The-C6H6/PLANTA-DE-ANILINA/PID/PDF/ENFRIADOR PRIMERA COLUMNA.pdf

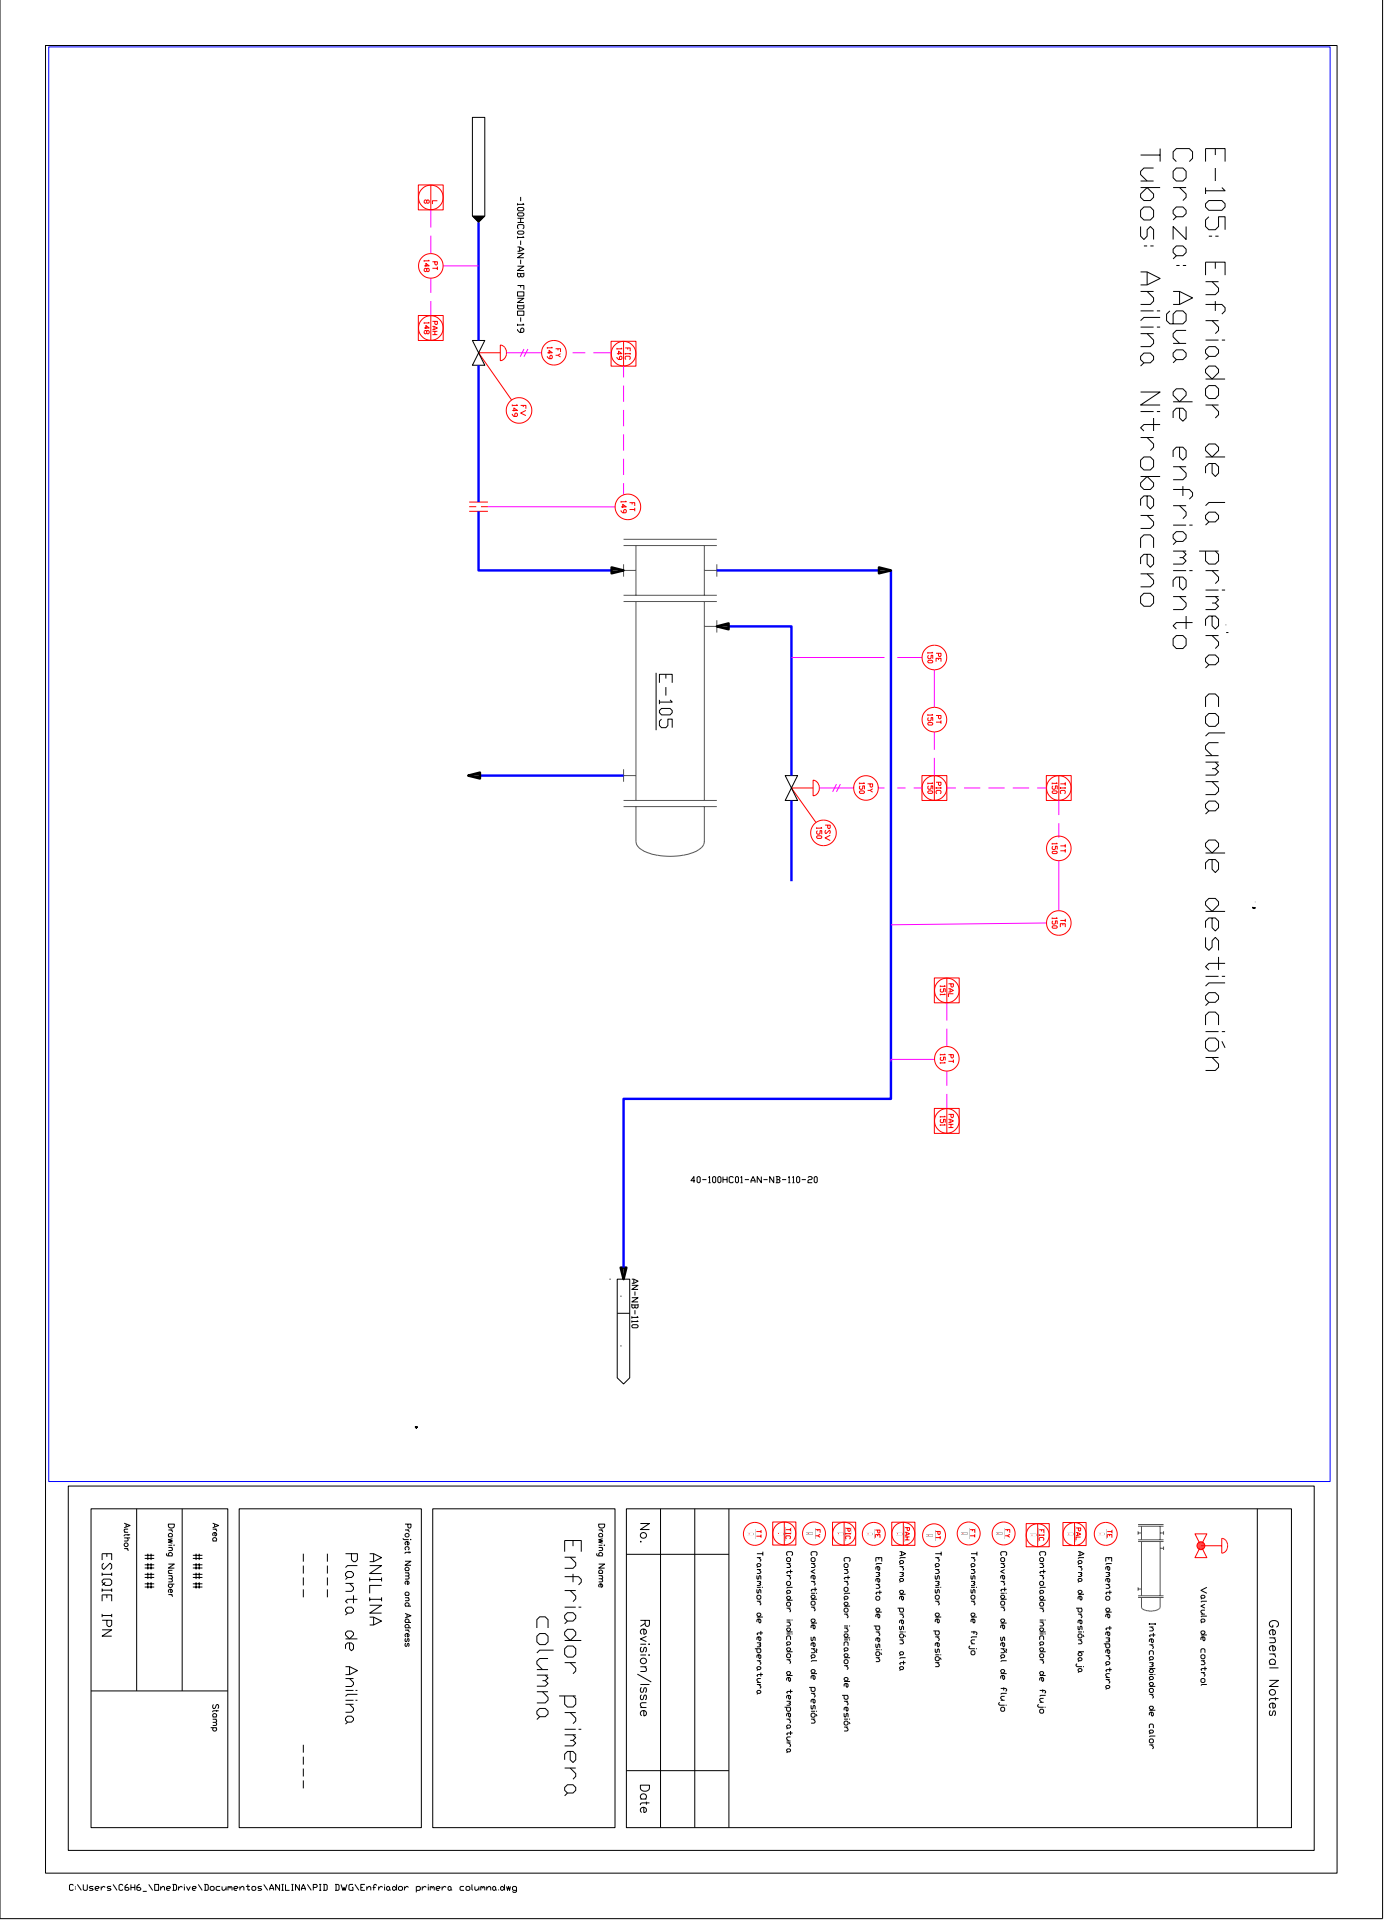
[picture p12: page 1]
