The-C6H6/PLANTA-DE-ANILINA/PID/PDF/INTERCAMBIADOR DE H2.pdf

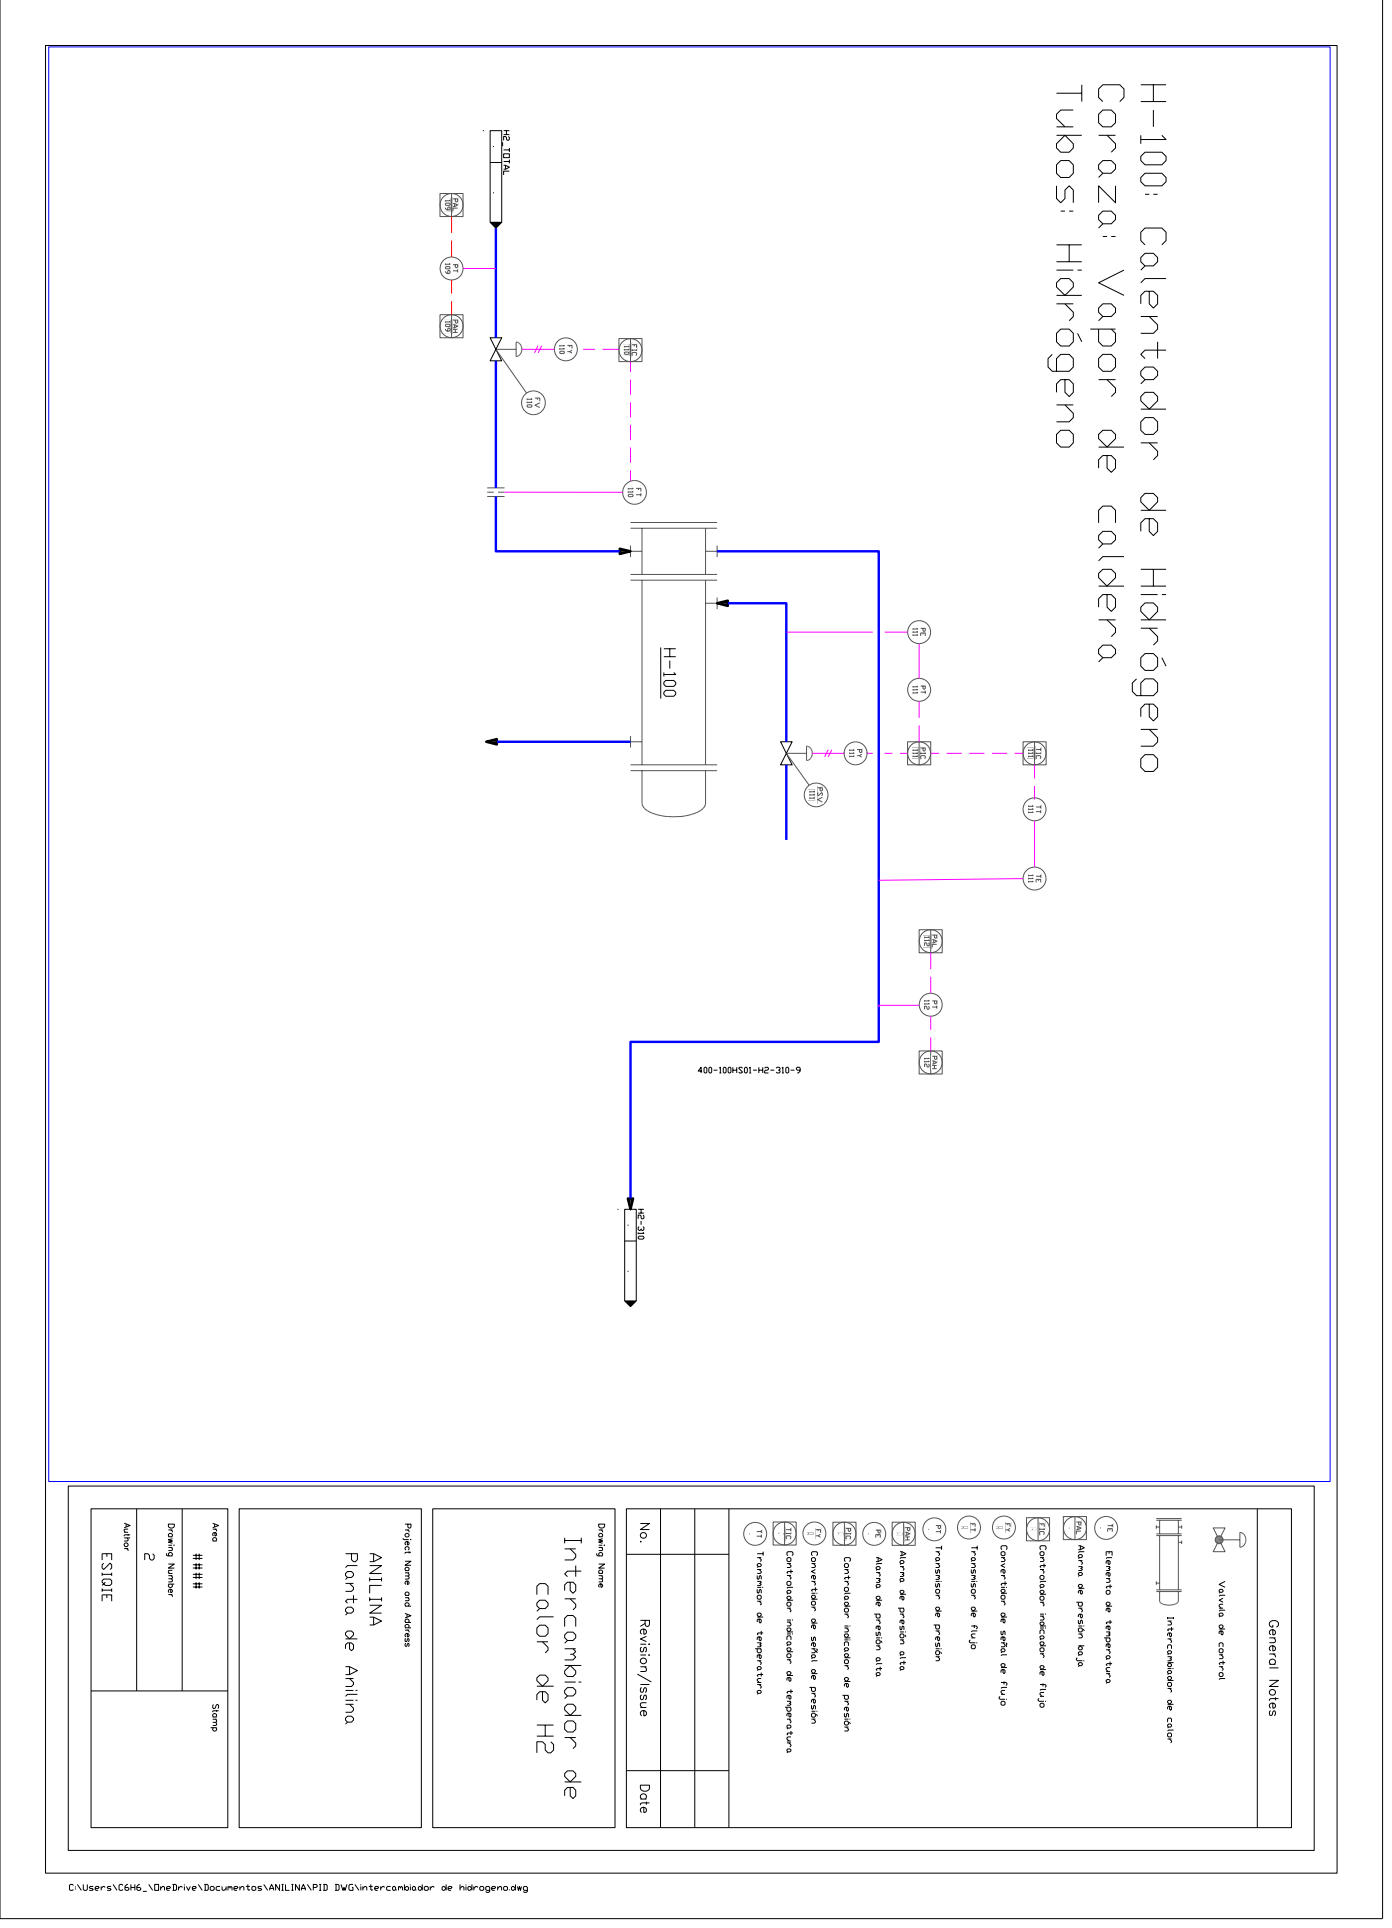
[picture p13: page 1]
