The-C6H6/PLANTA-DE-ANILINA/PID/PDF/INTERCAMBIADOR DE MEZCLA.pdf

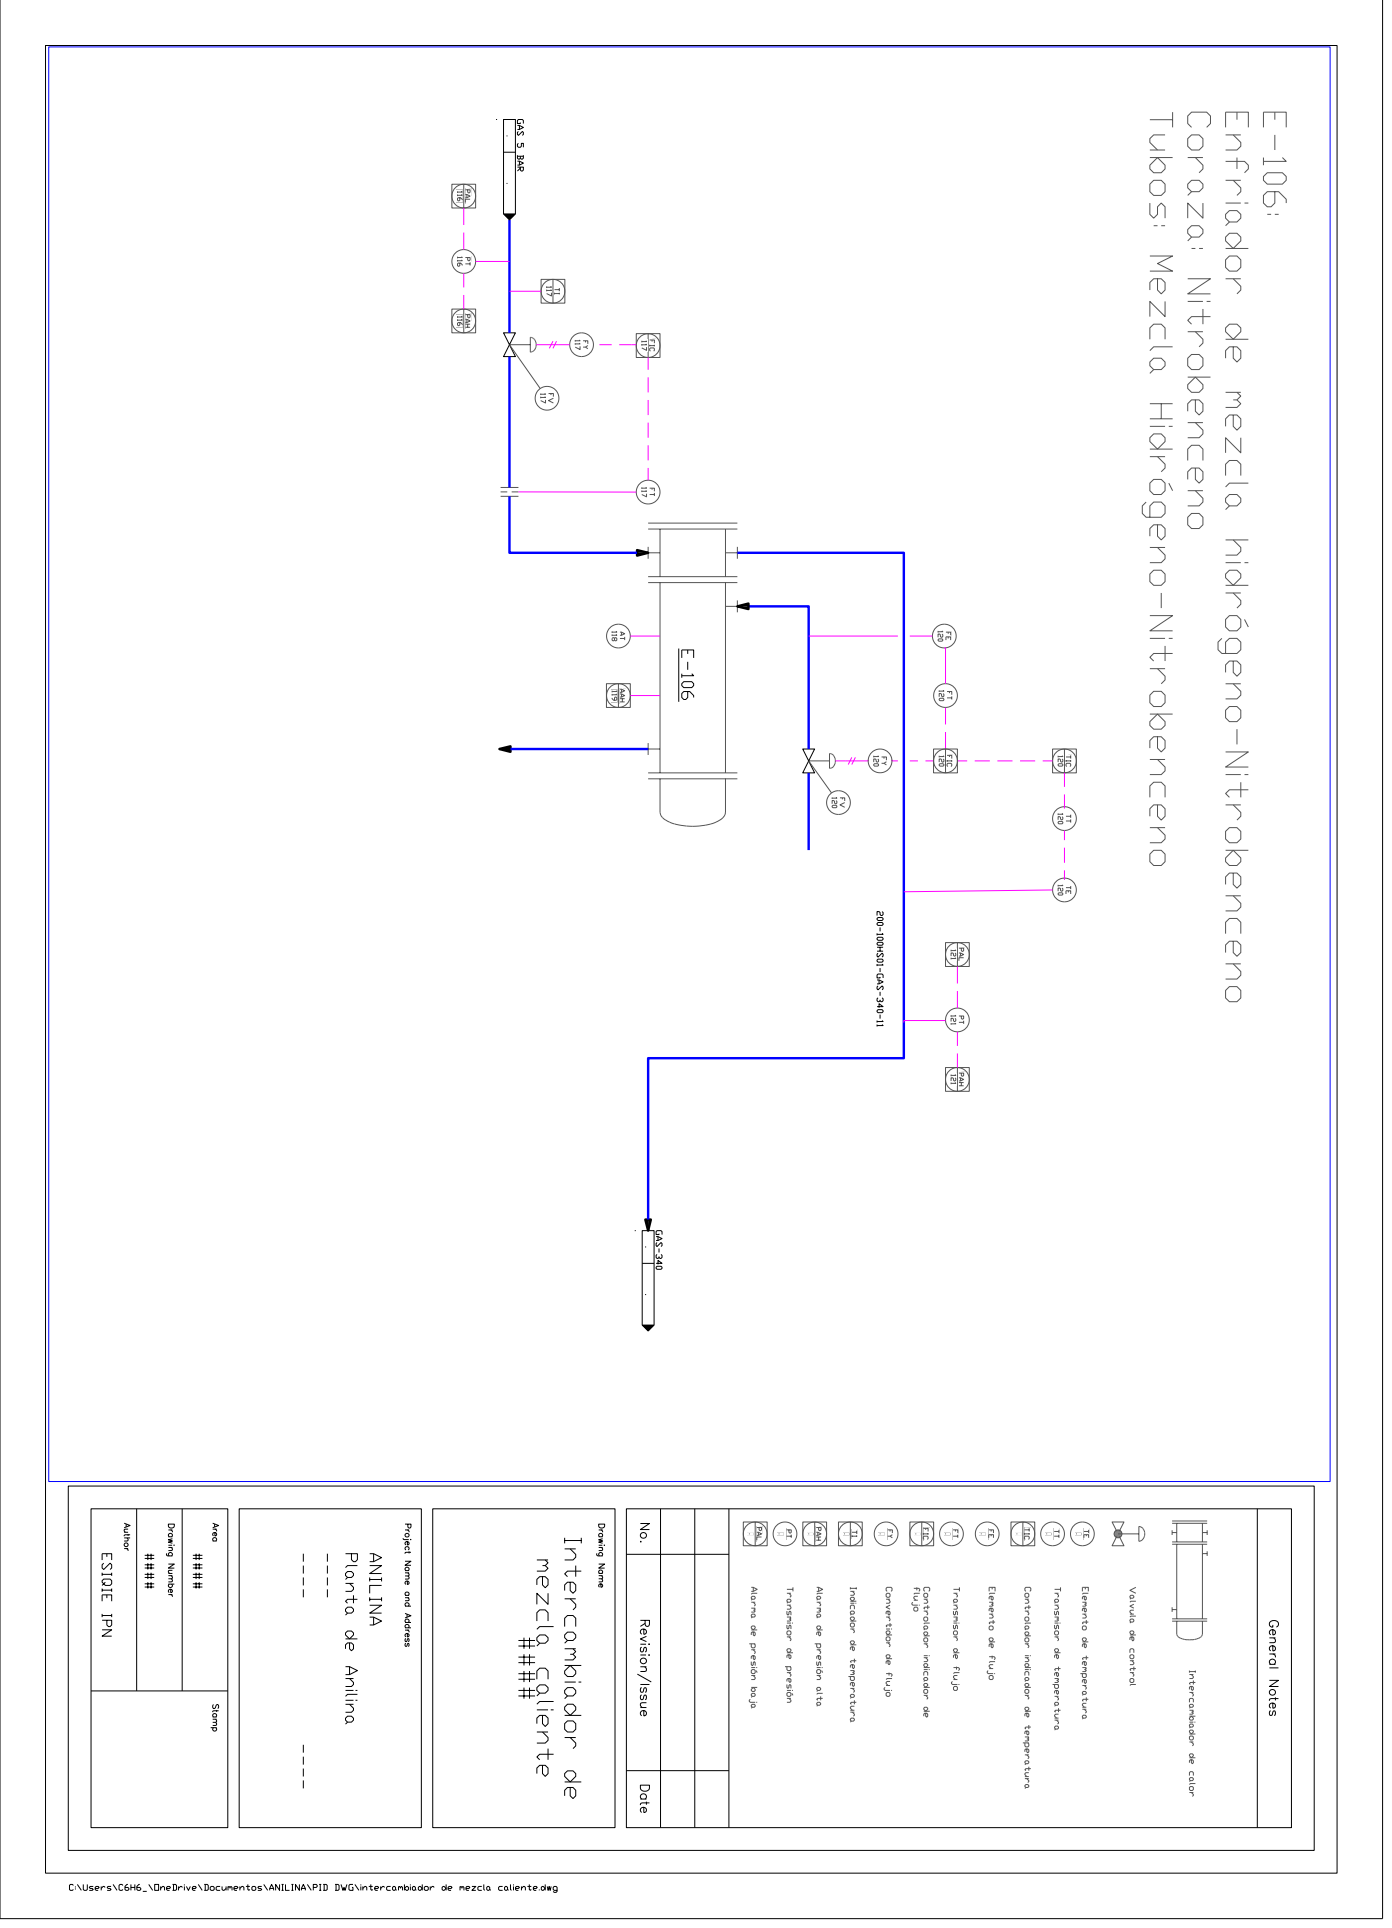
[picture p14: page 1]
