The-C6H6/PLANTA-DE-ANILINA/PID/PDF/INTERCAMBIADOR DESPUES DE REACTOR.pdf

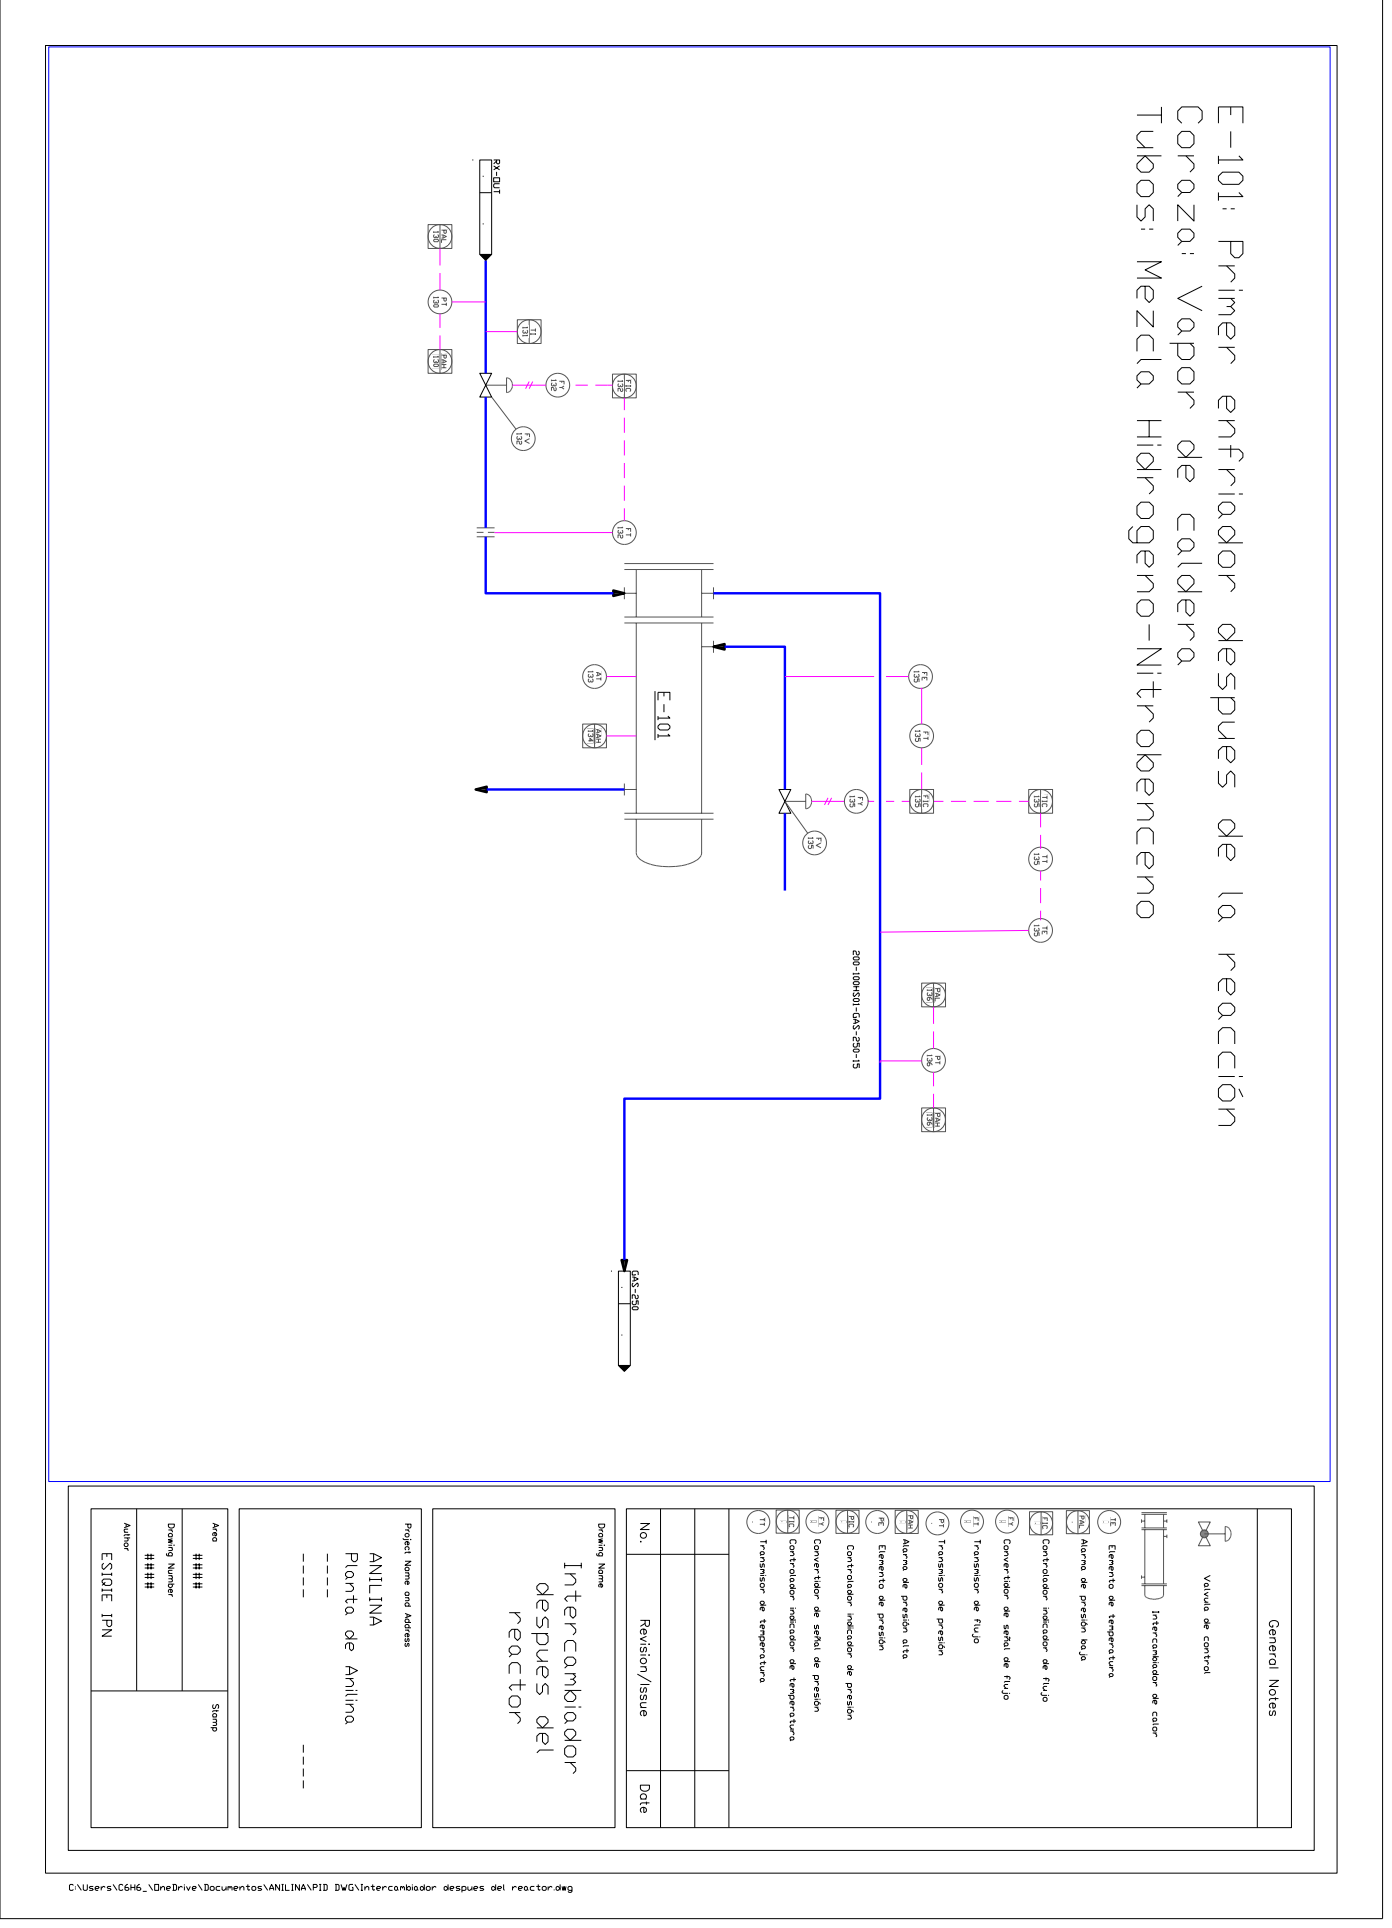
[picture p15: page 1]
