The-C6H6/PLANTA-DE-ANILINA/PID/PDF/INTERCAMBIADOR DESPUES NITROBENCENO.pdf

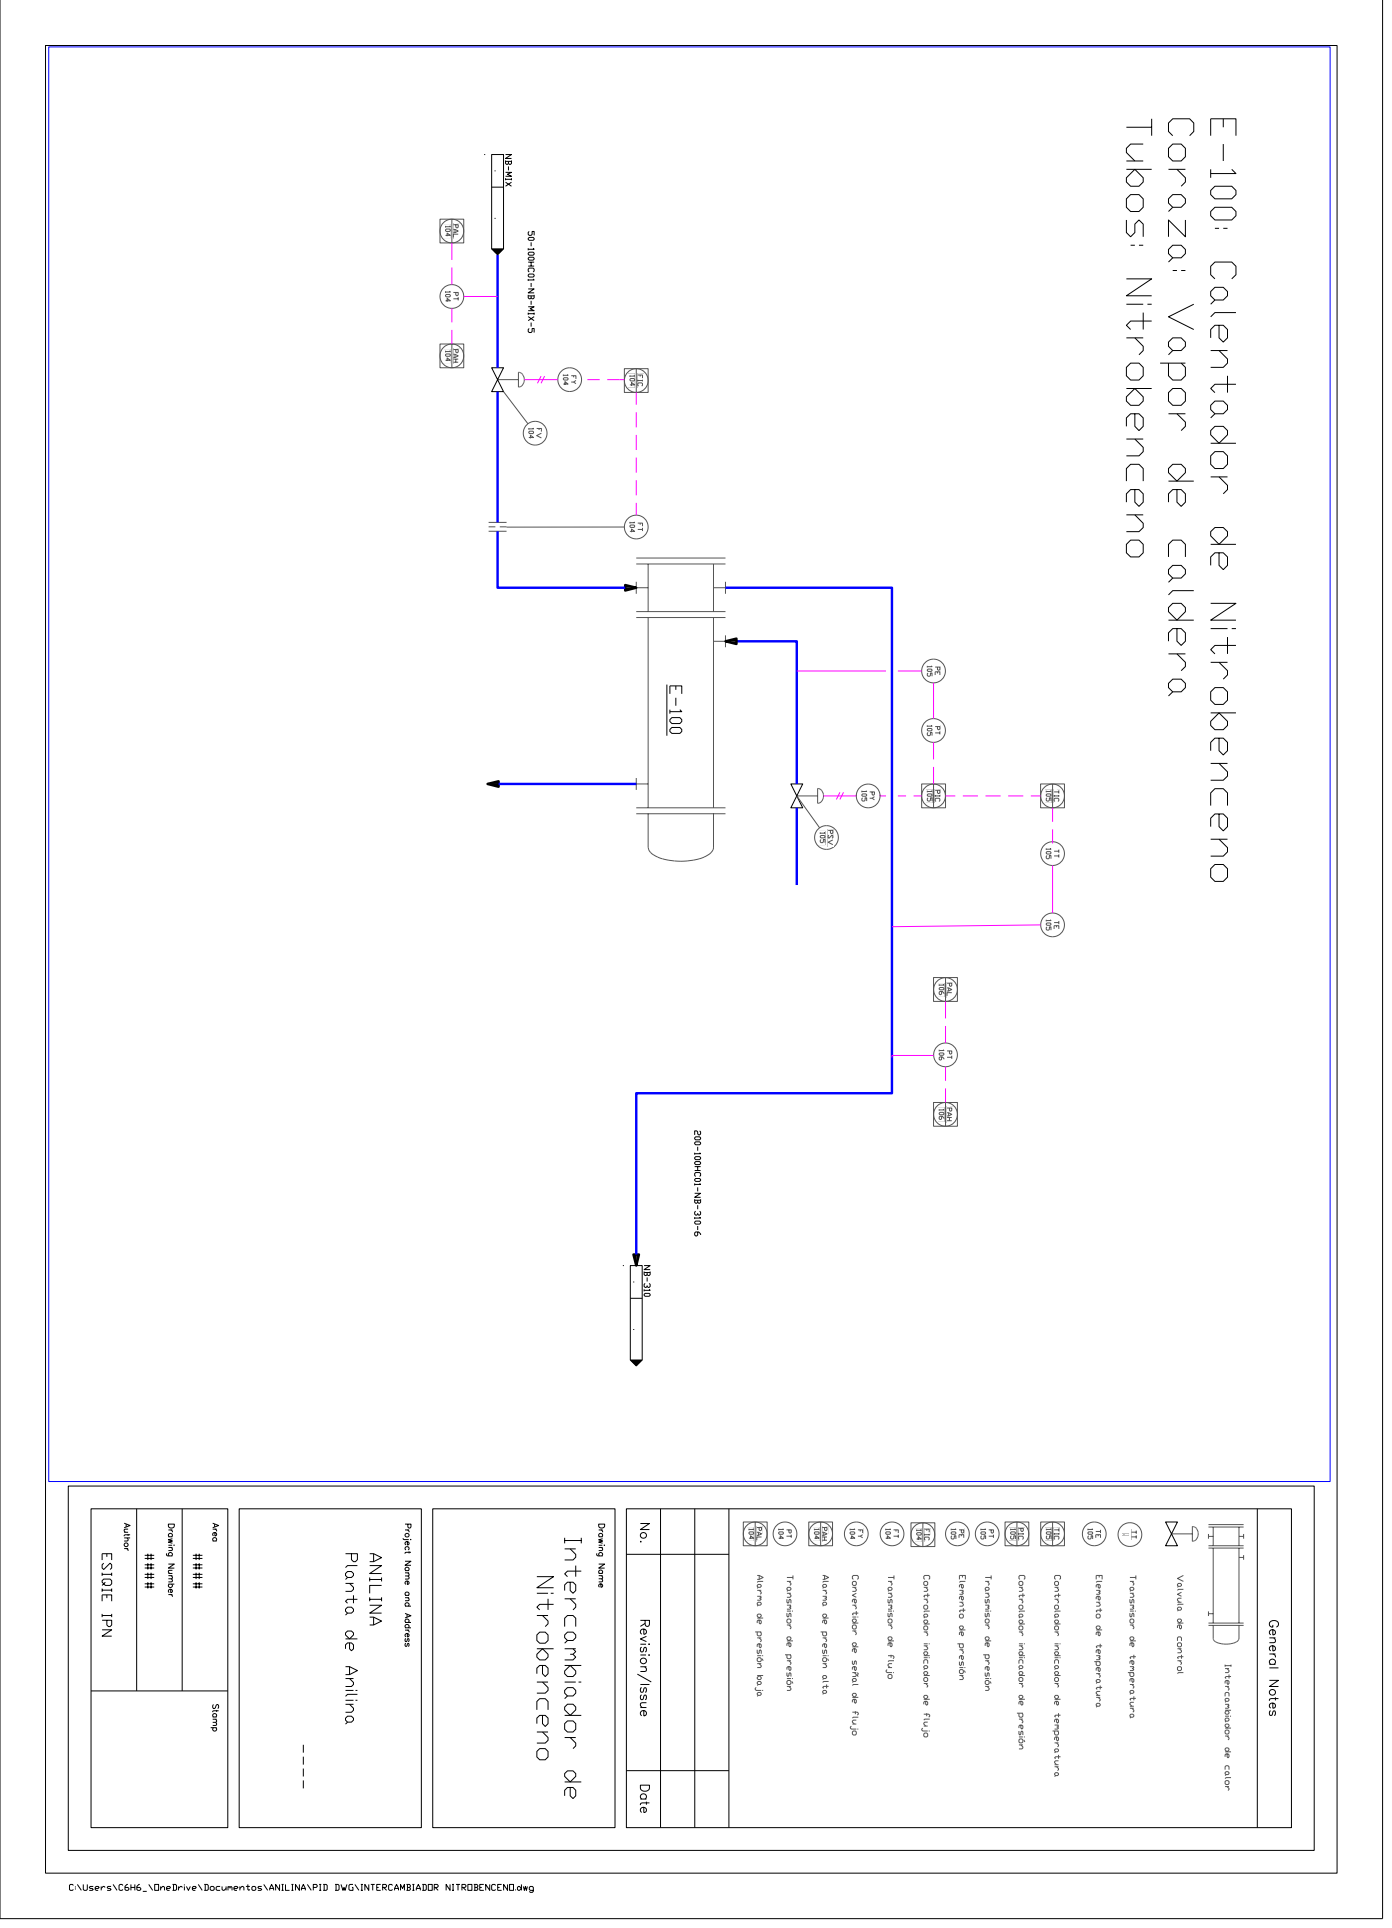
[picture p16: page 1]
