The-C6H6/PLANTA-DE-ANILINA/PID/PDF/MIXER 102.pdf

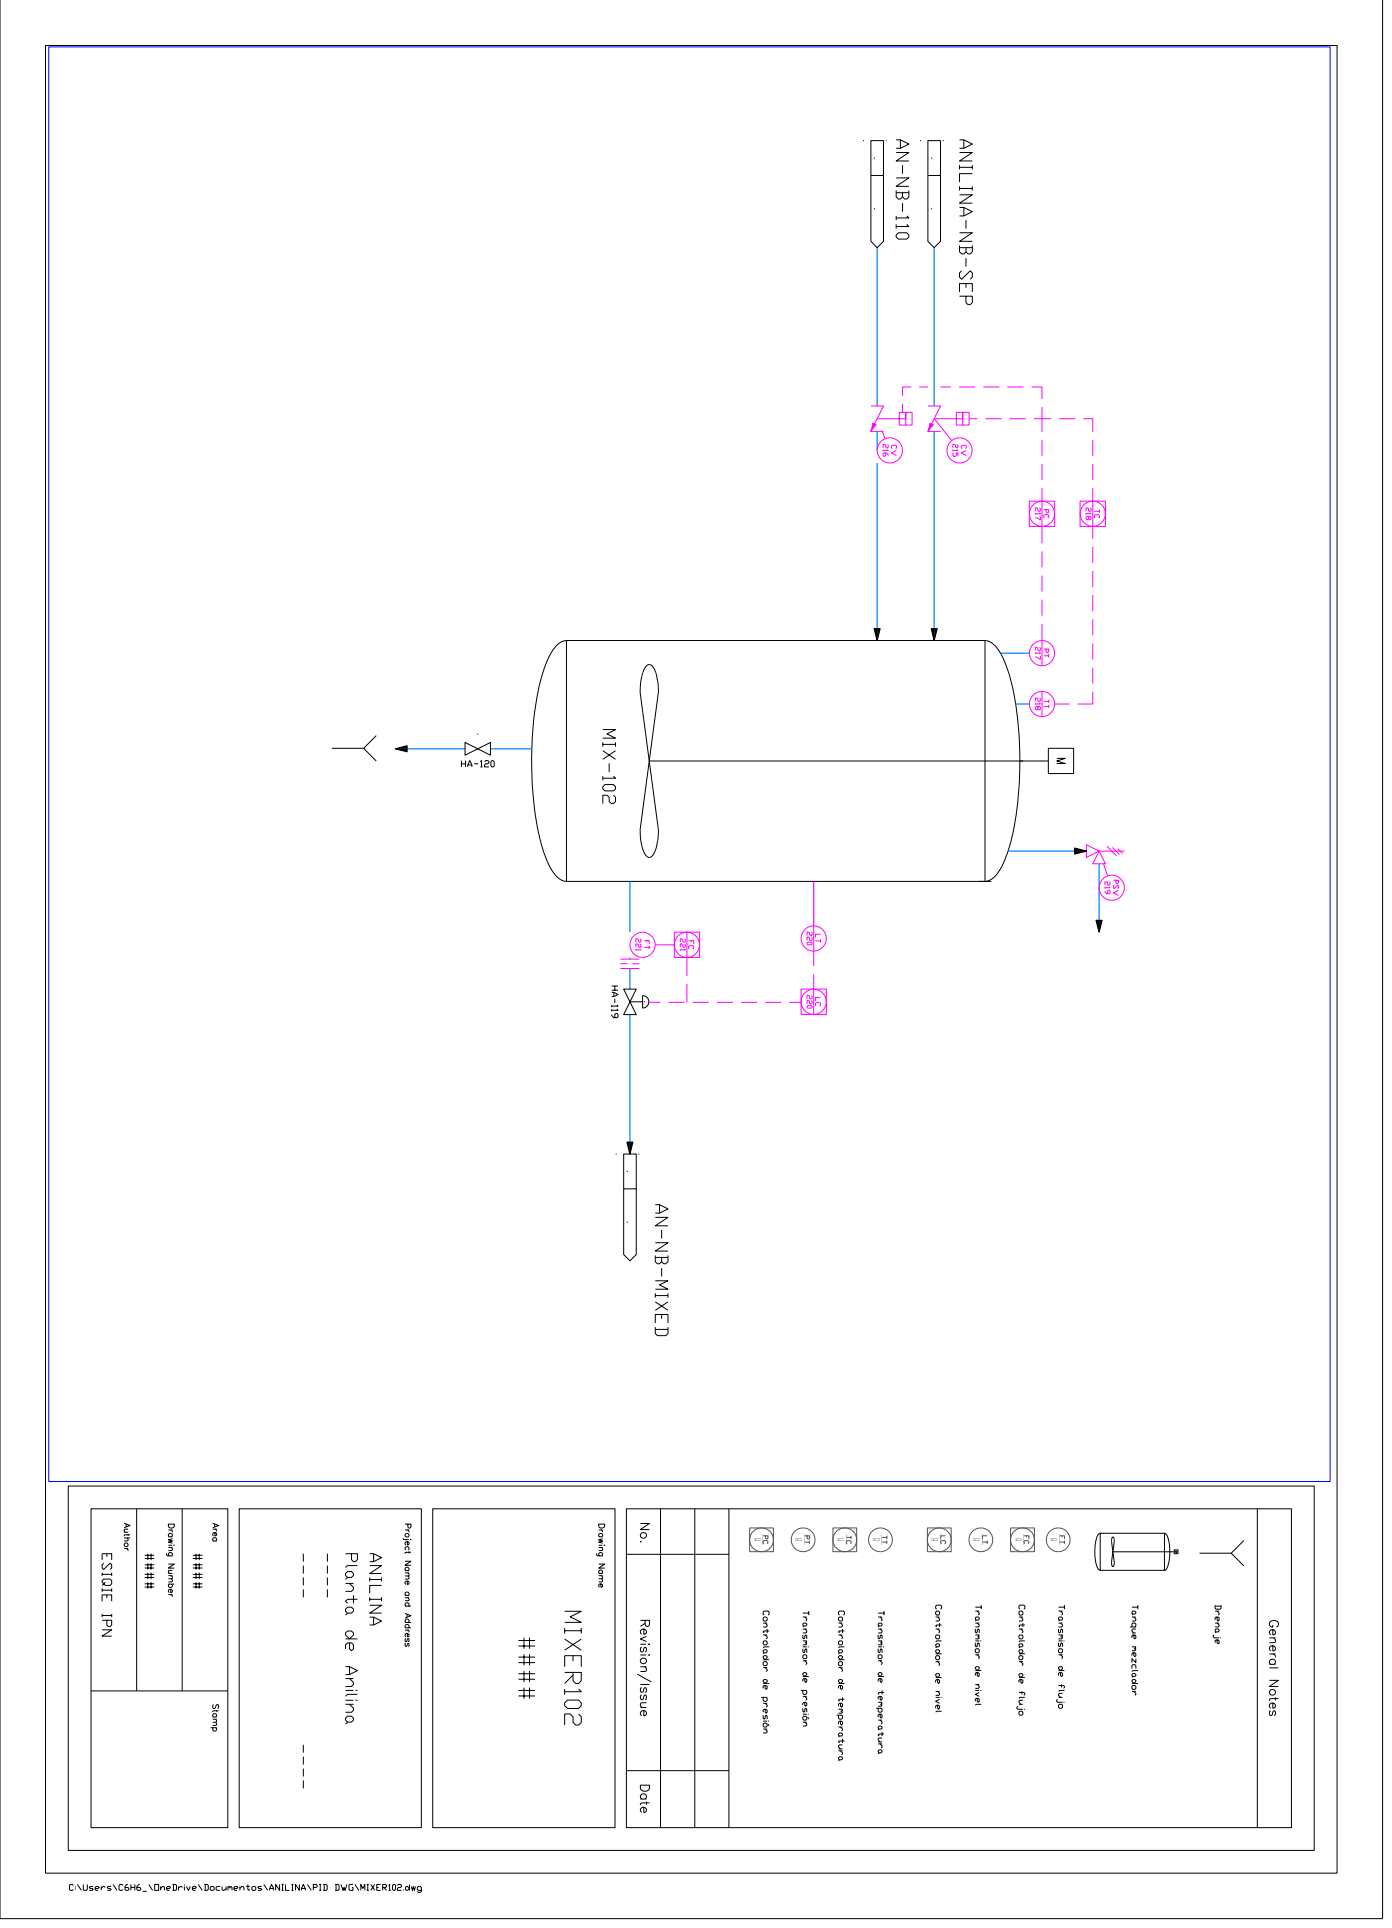
[picture p17: page 1]
