The-C6H6/PLANTA-DE-ANILINA/PID/PDF/REACTOR ENCHAQUETADO.pdf

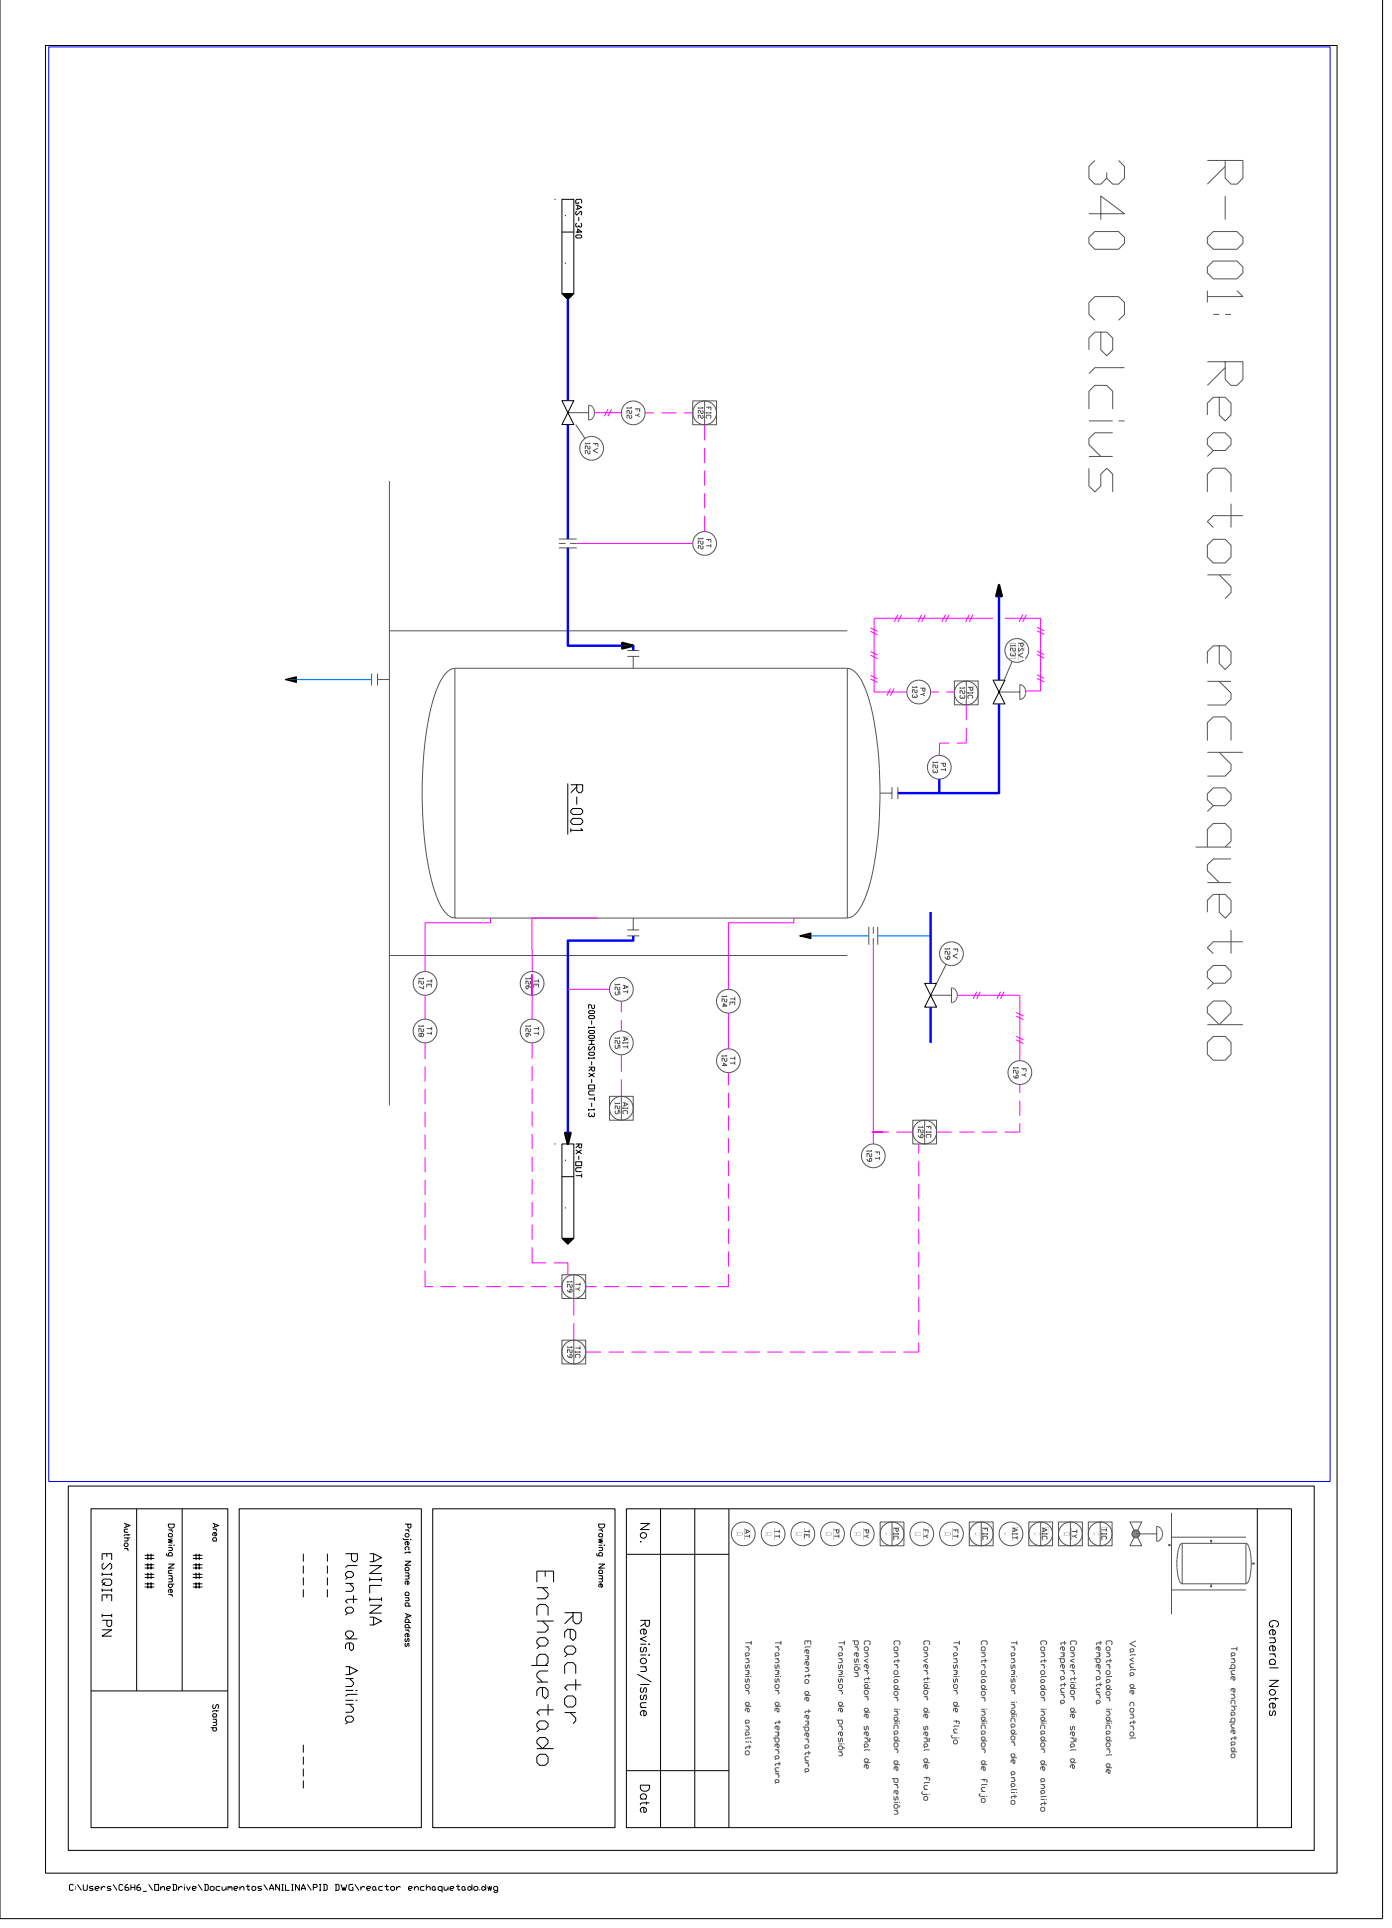
[picture p18: page 1]
