The-C6H6/PLANTA-DE-ANILINA/PID/PDF/SEGUNDO ENFRIADOR.pdf

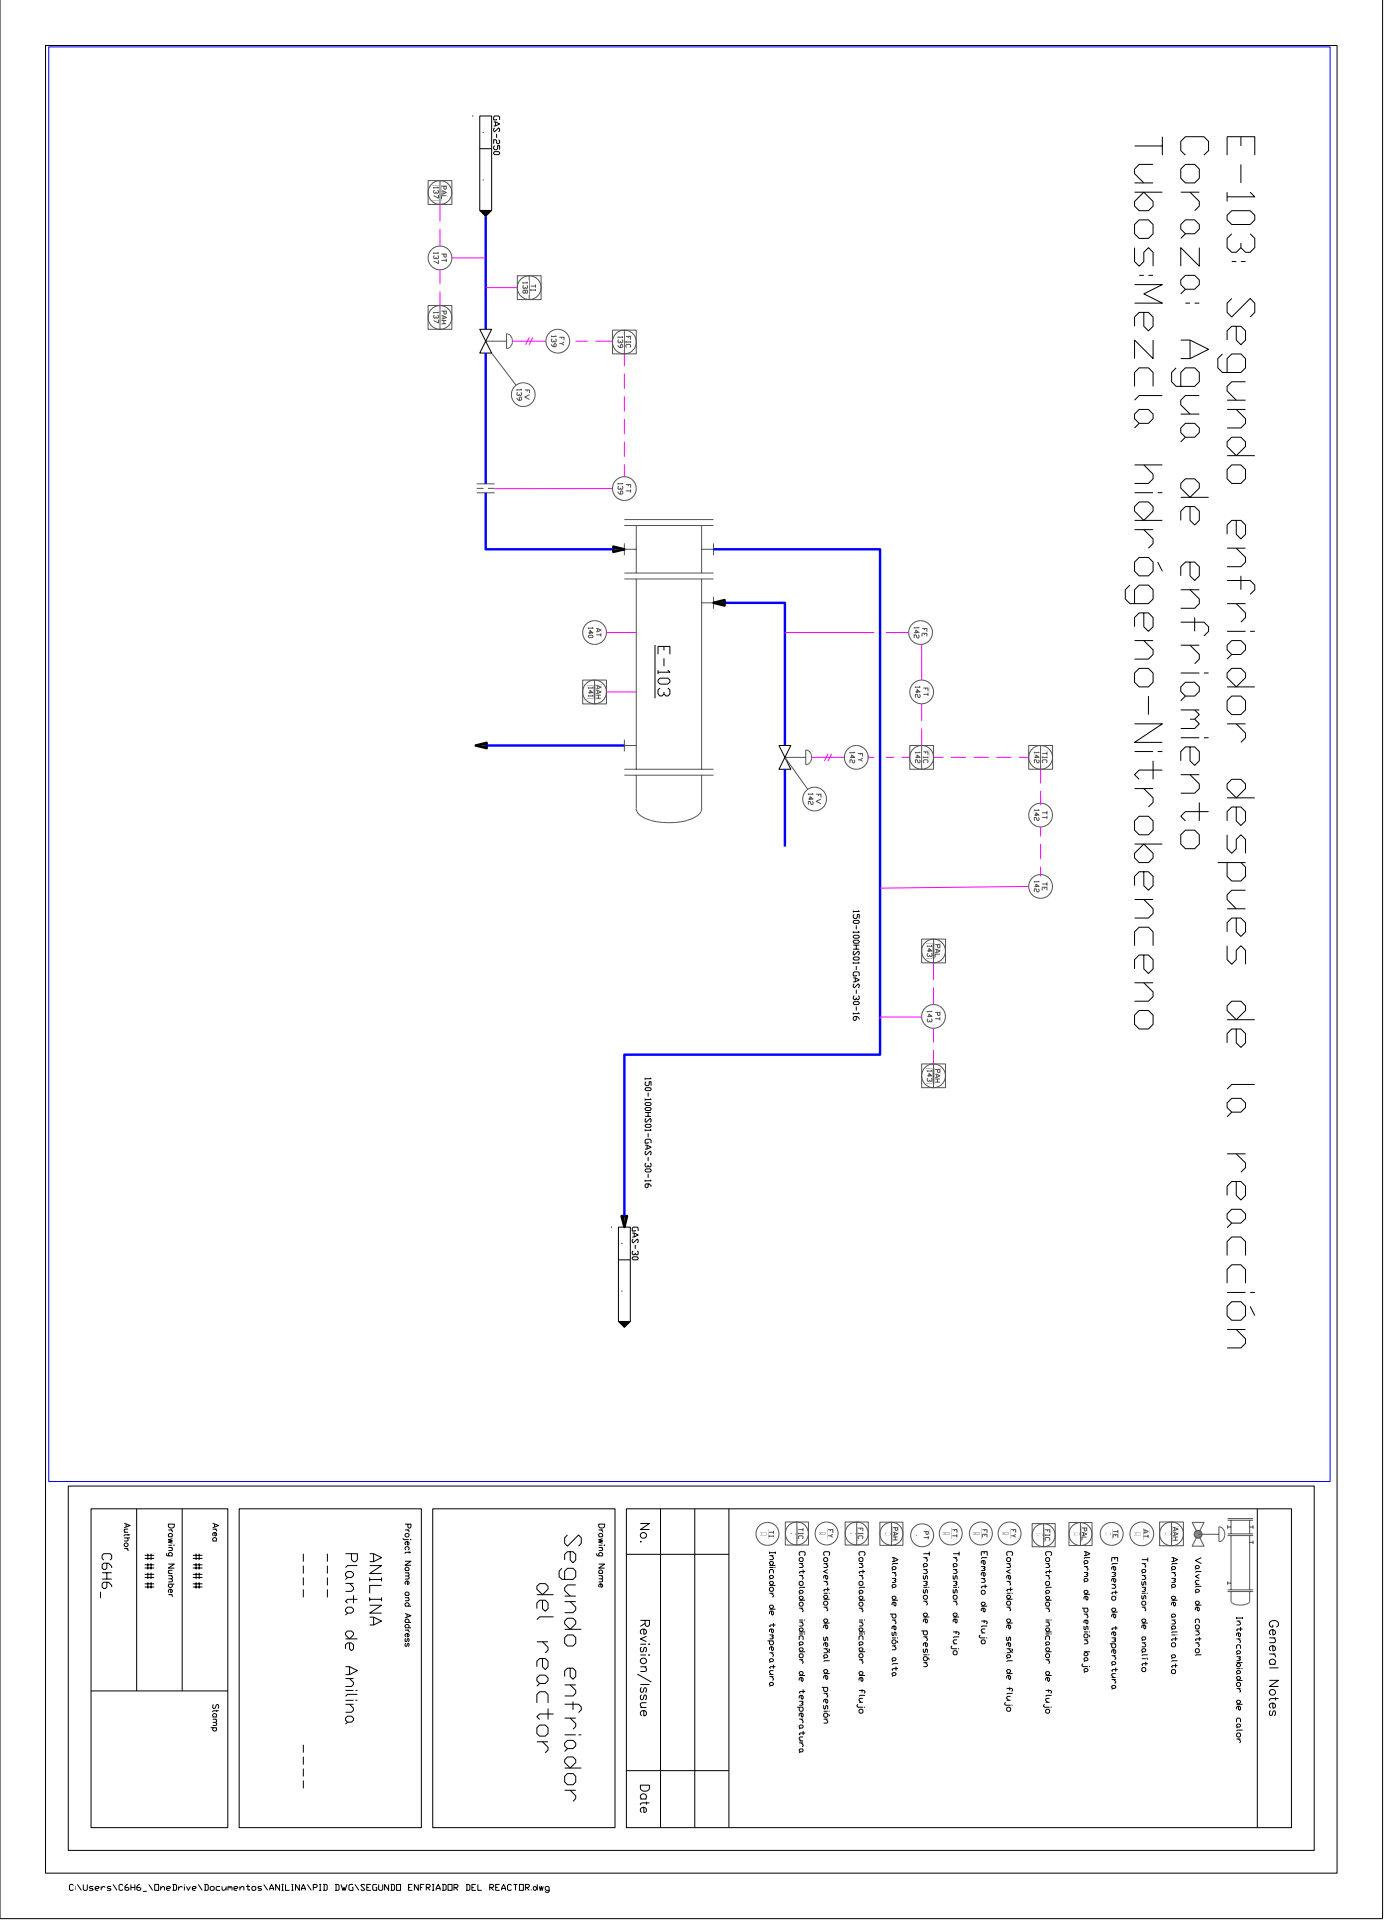
[picture p19: page 1]
