The-C6H6/PLANTA-DE-ANILINA/PID/PDF/SEPARADOR001.pdf

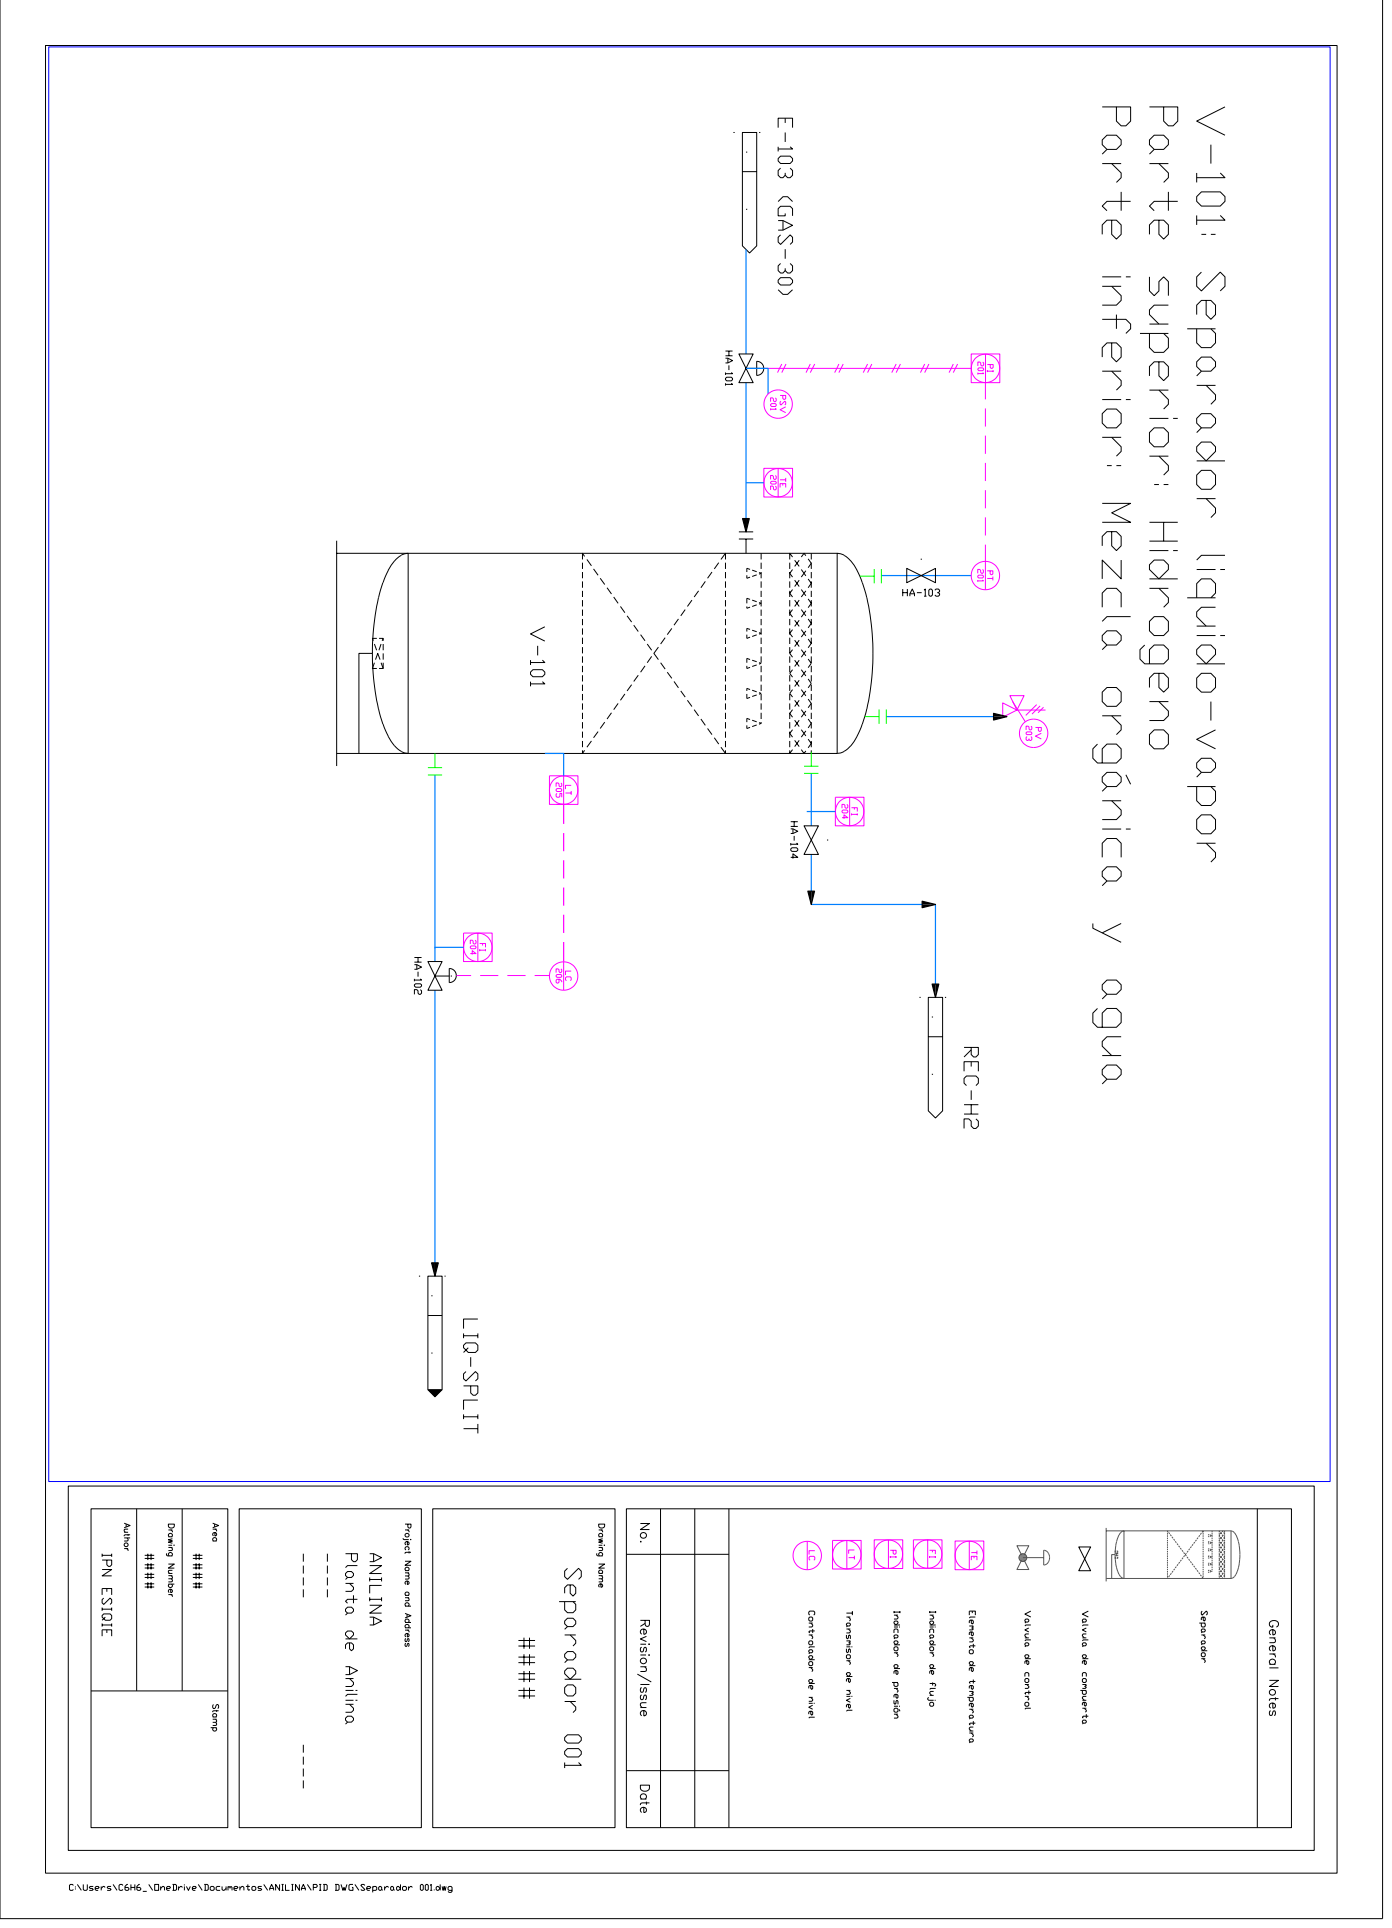
[picture p20: page 1]
