The-C6H6/PLANTA-DE-ANILINA/PID/PDF/TANQUE DE HIDROGENO.pdf

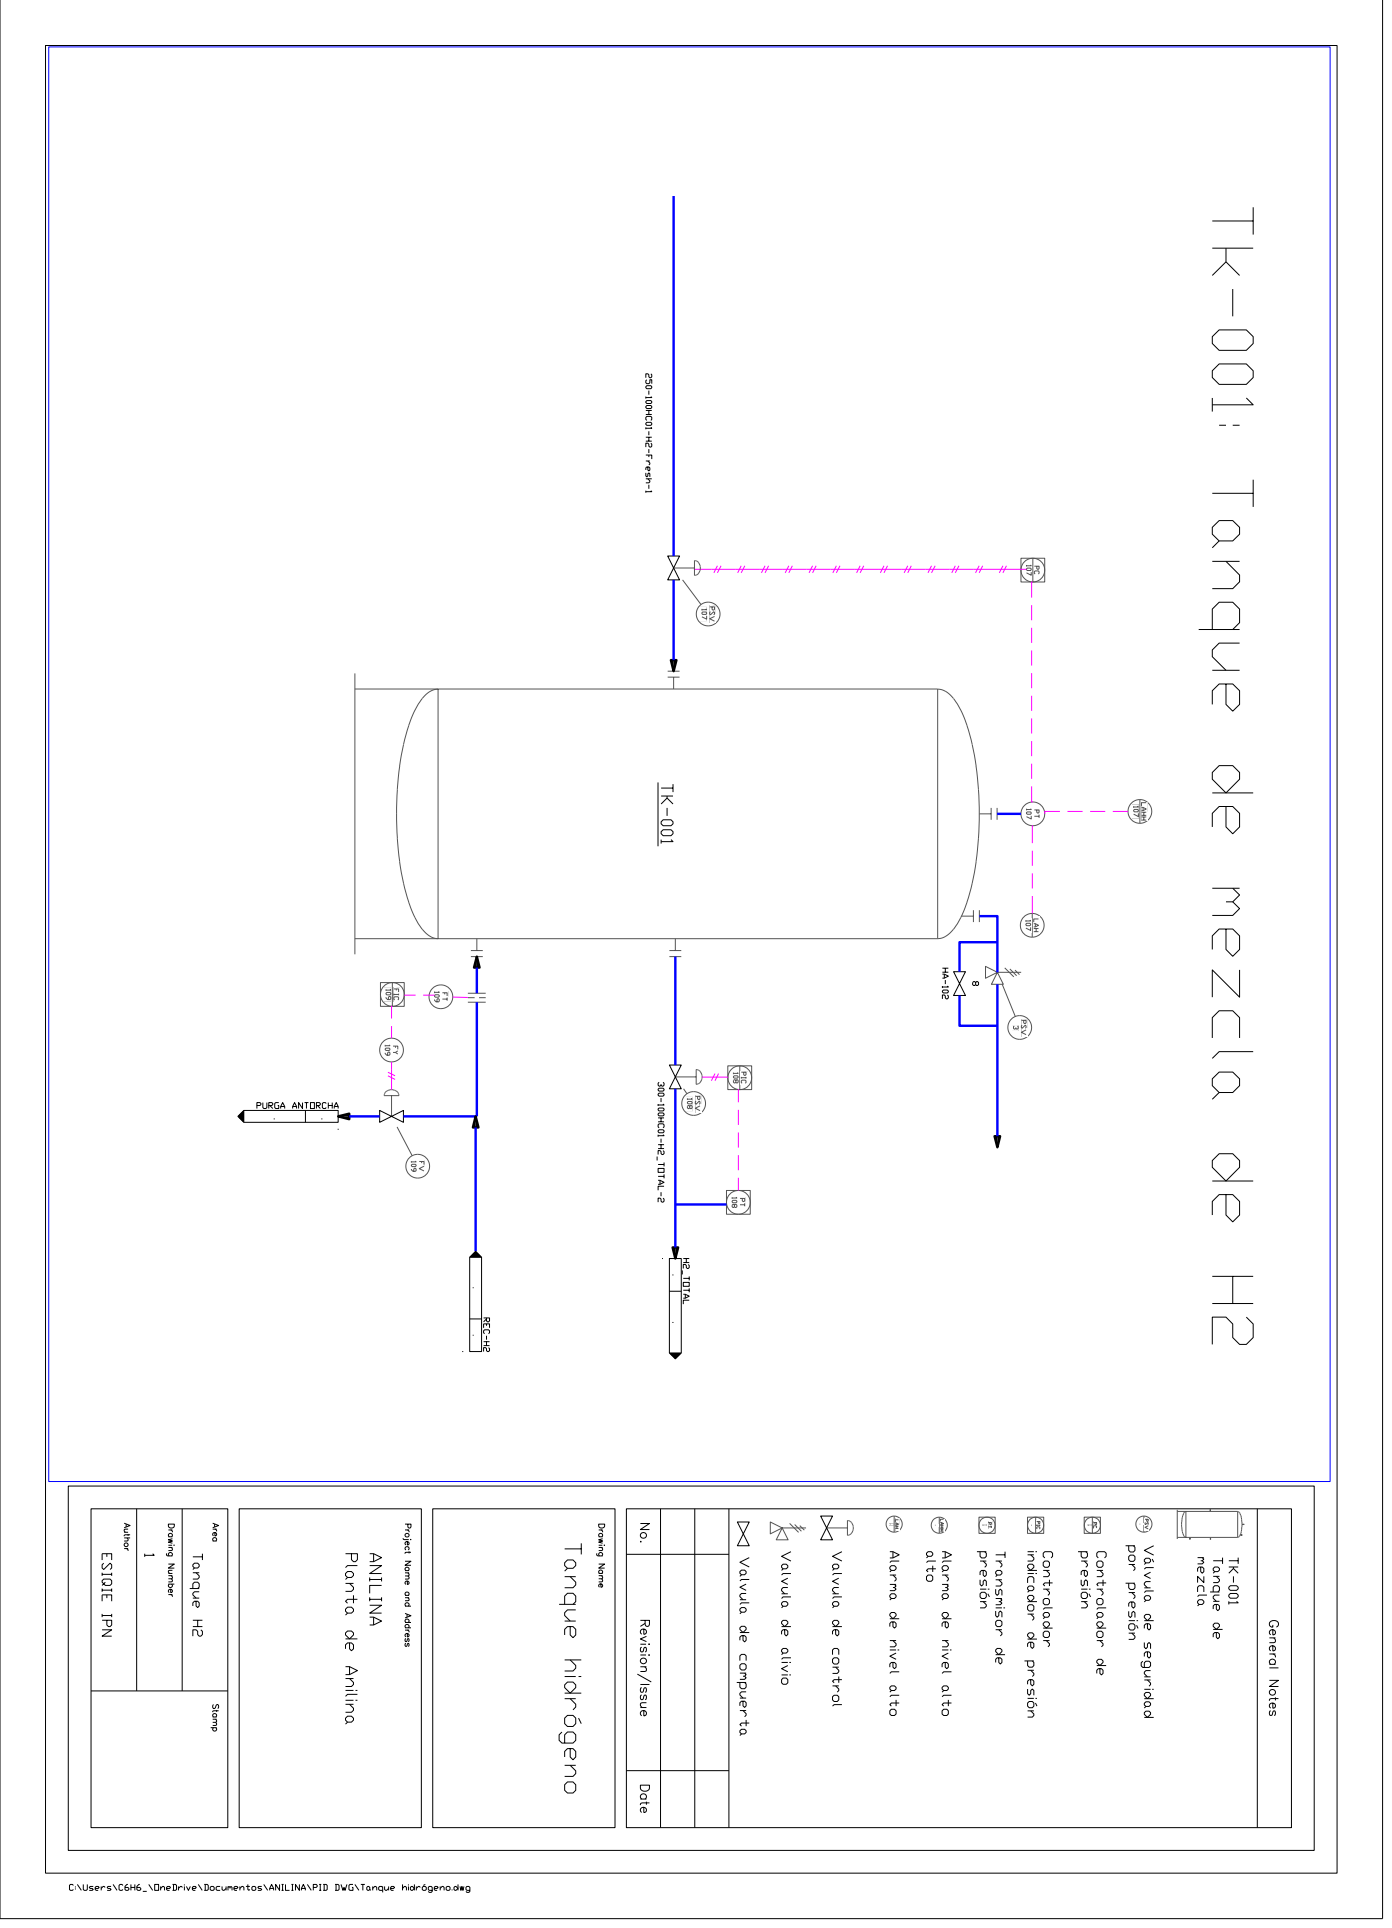
[picture p21: page 1]
