The-C6H6/PLANTA-DE-ANILINA/PID/PDF/TANQUE DE NITROBENCENO.pdf

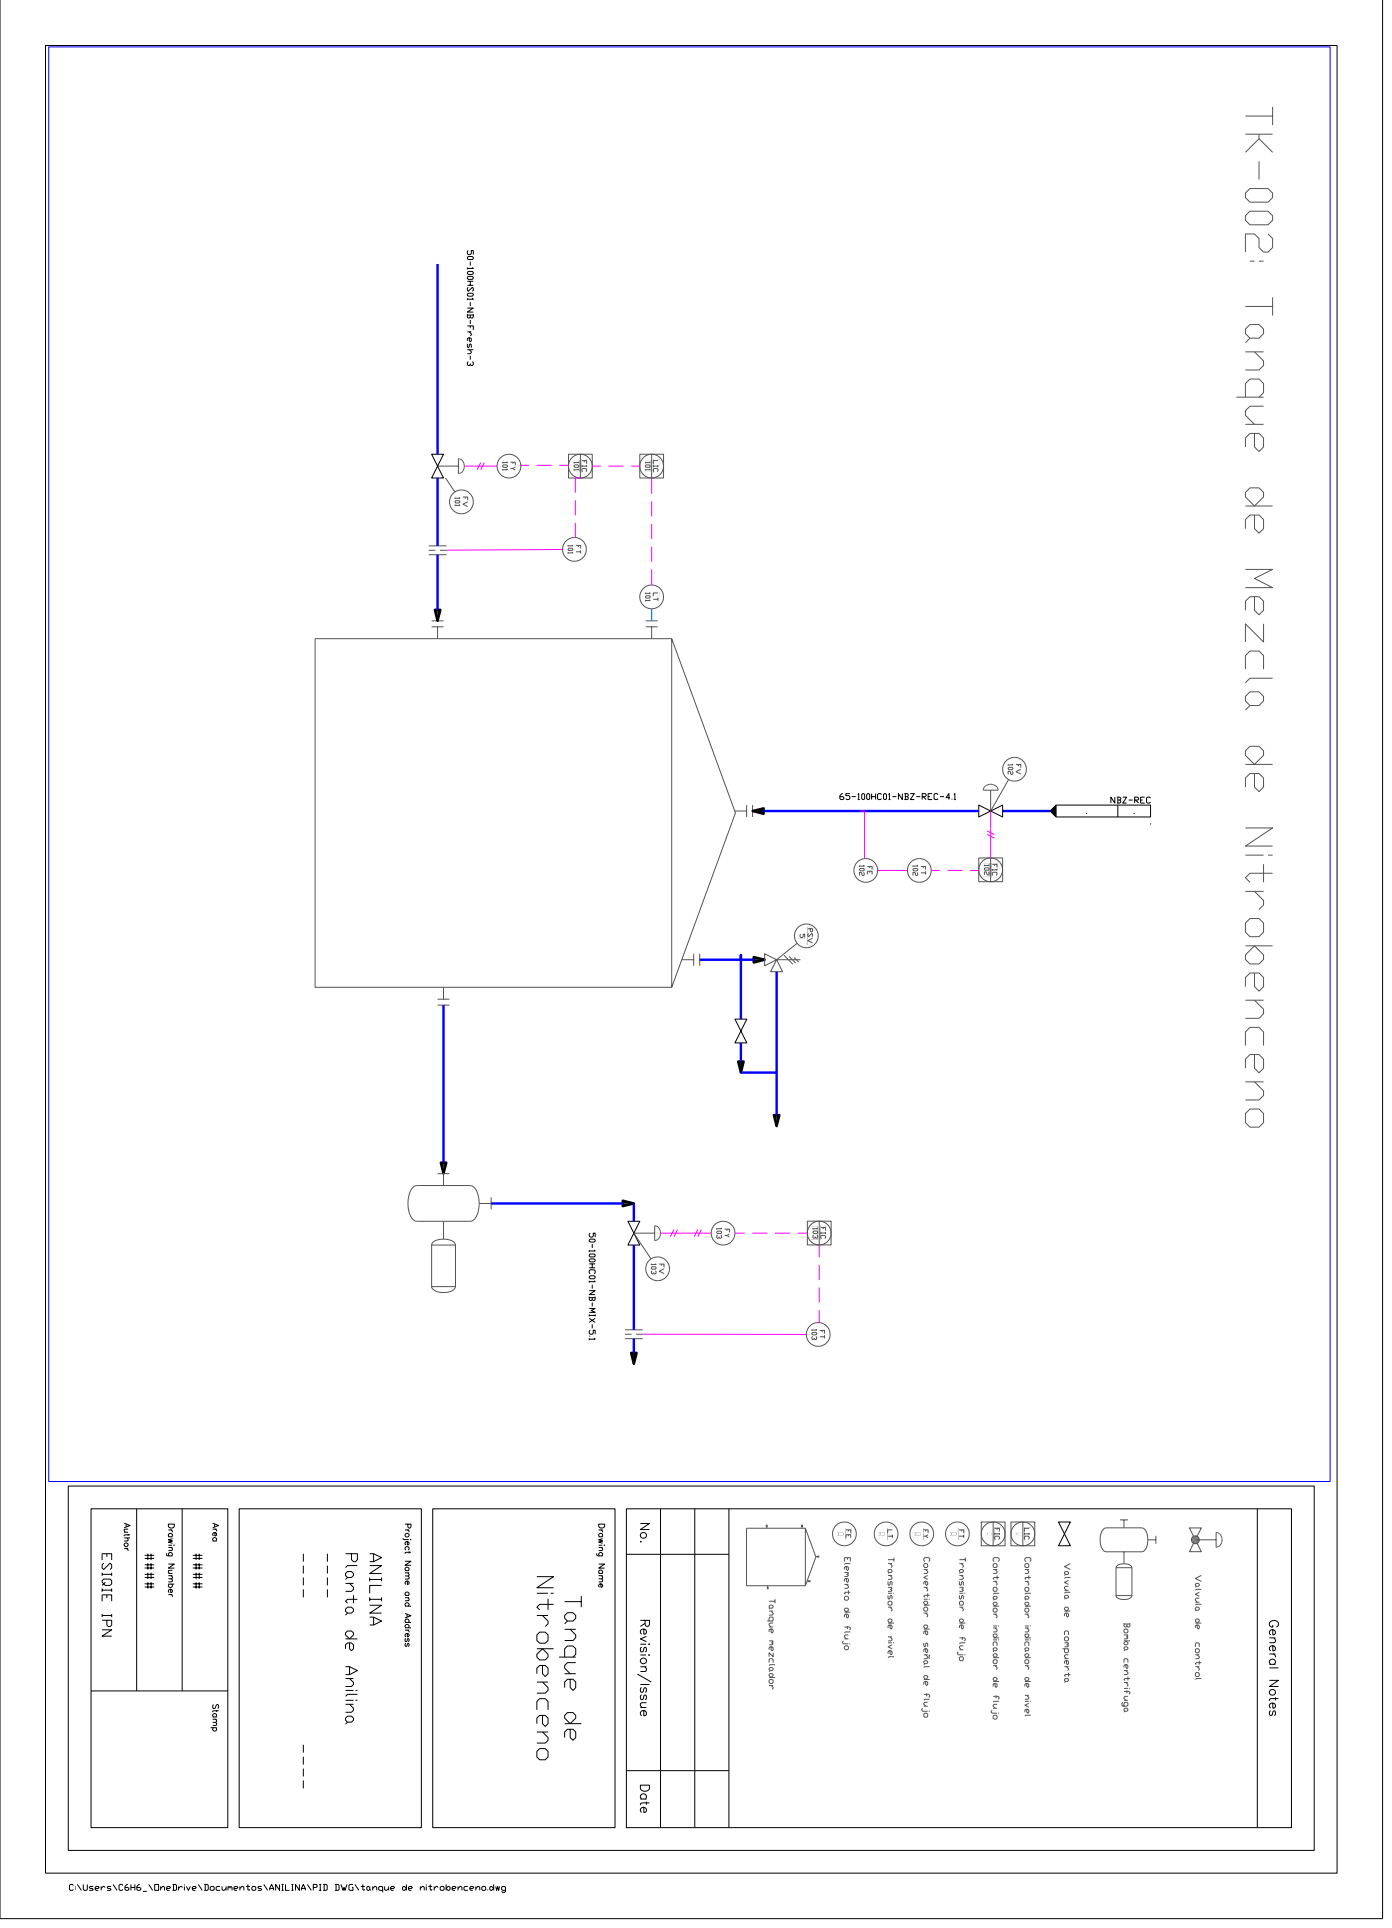
[picture p22: page 1]
