The-C6H6/PLANTA-DE-ANILINA/PID/PDF/TORCH.pdf

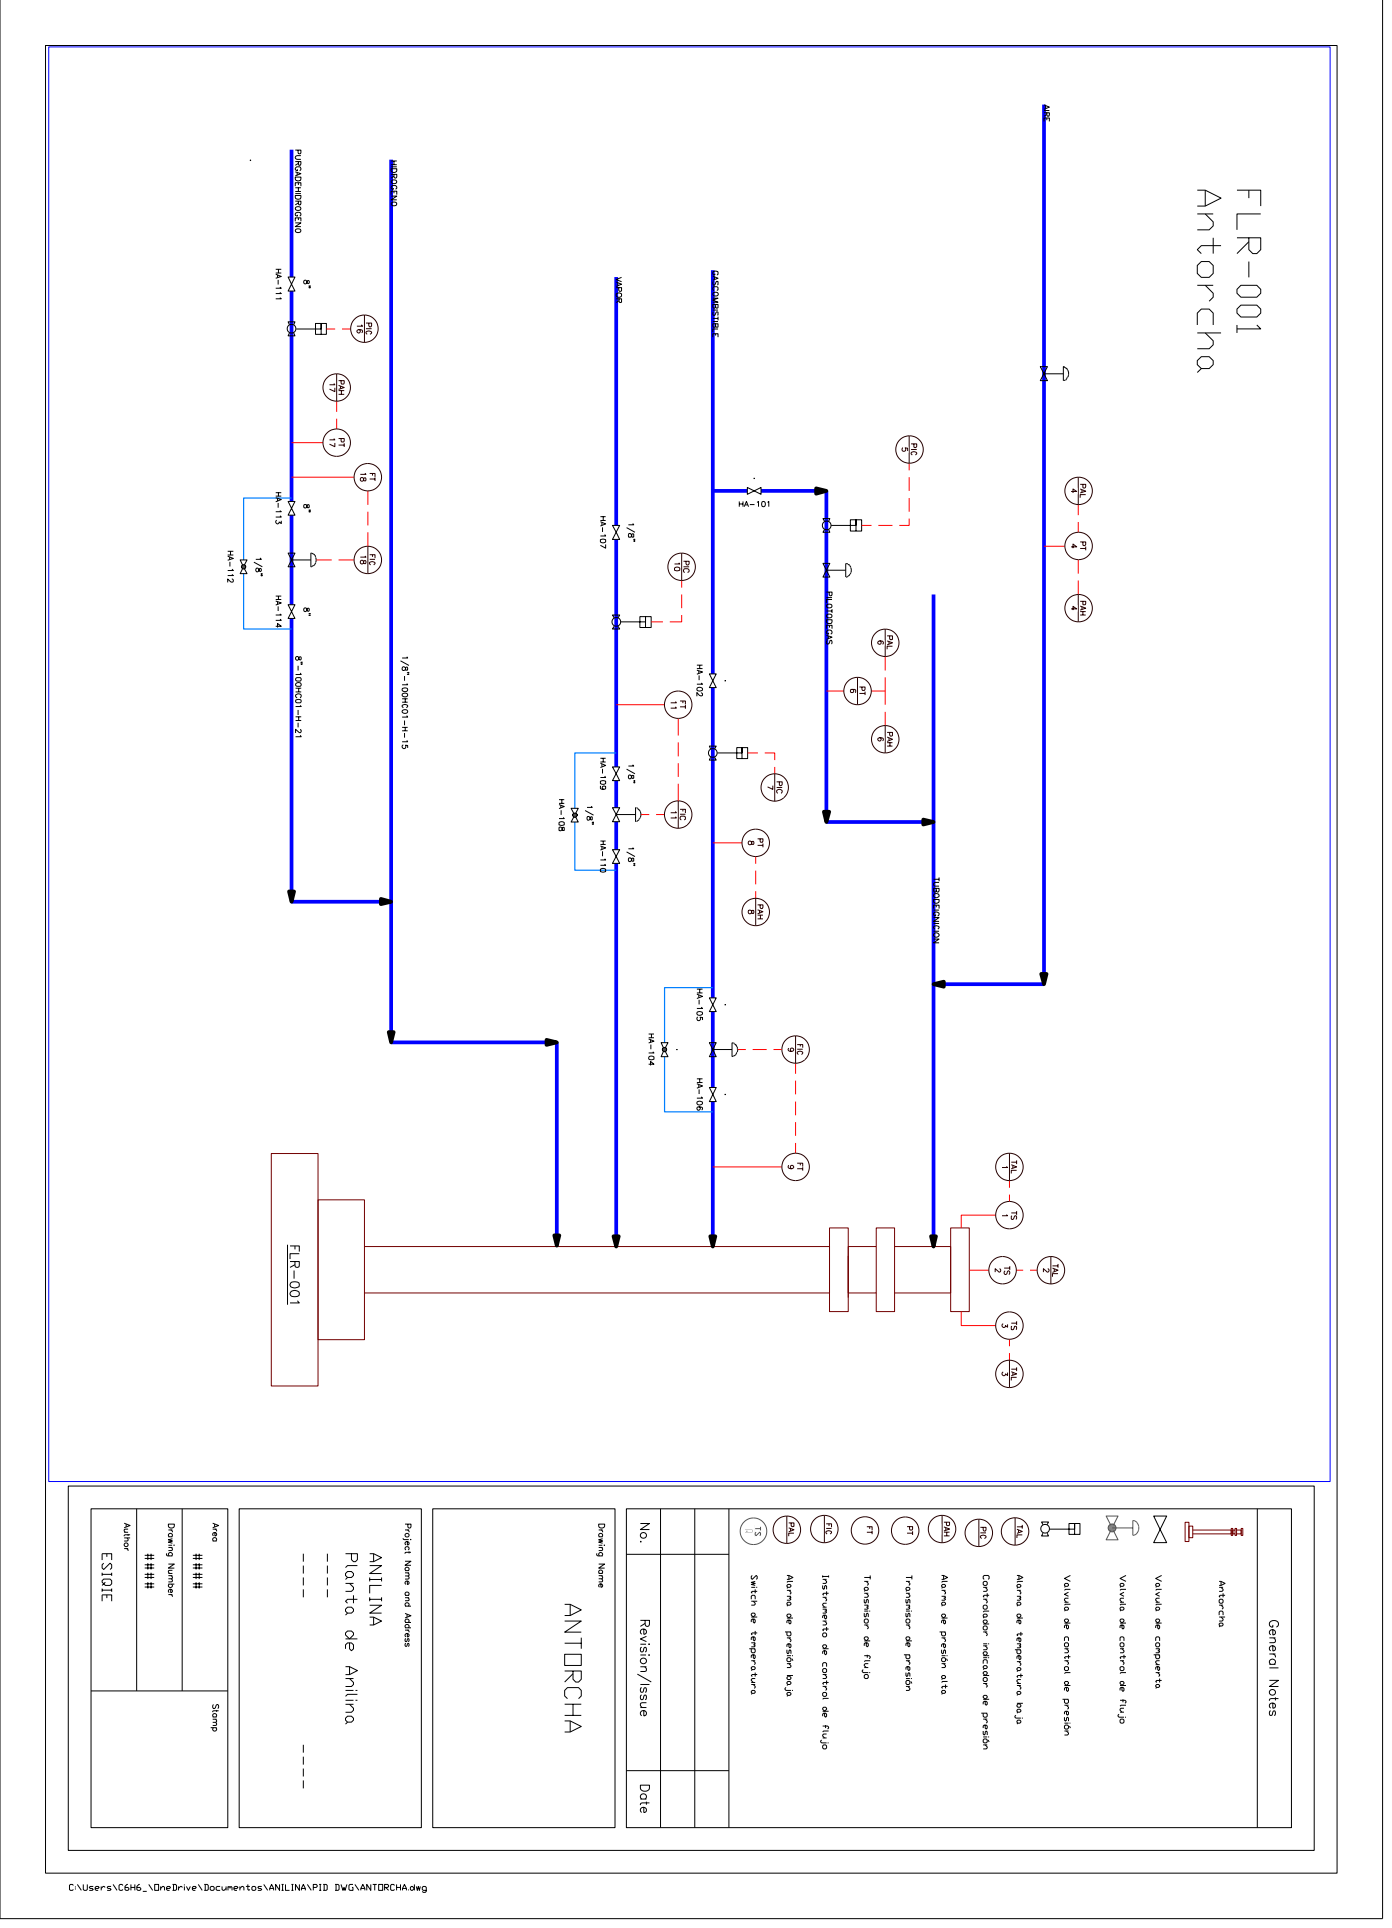
[picture p23: page 1]
