The-C6H6/PLANTA-DE-ANILINA/PID/PDF/DECANTADOR V100.pdf

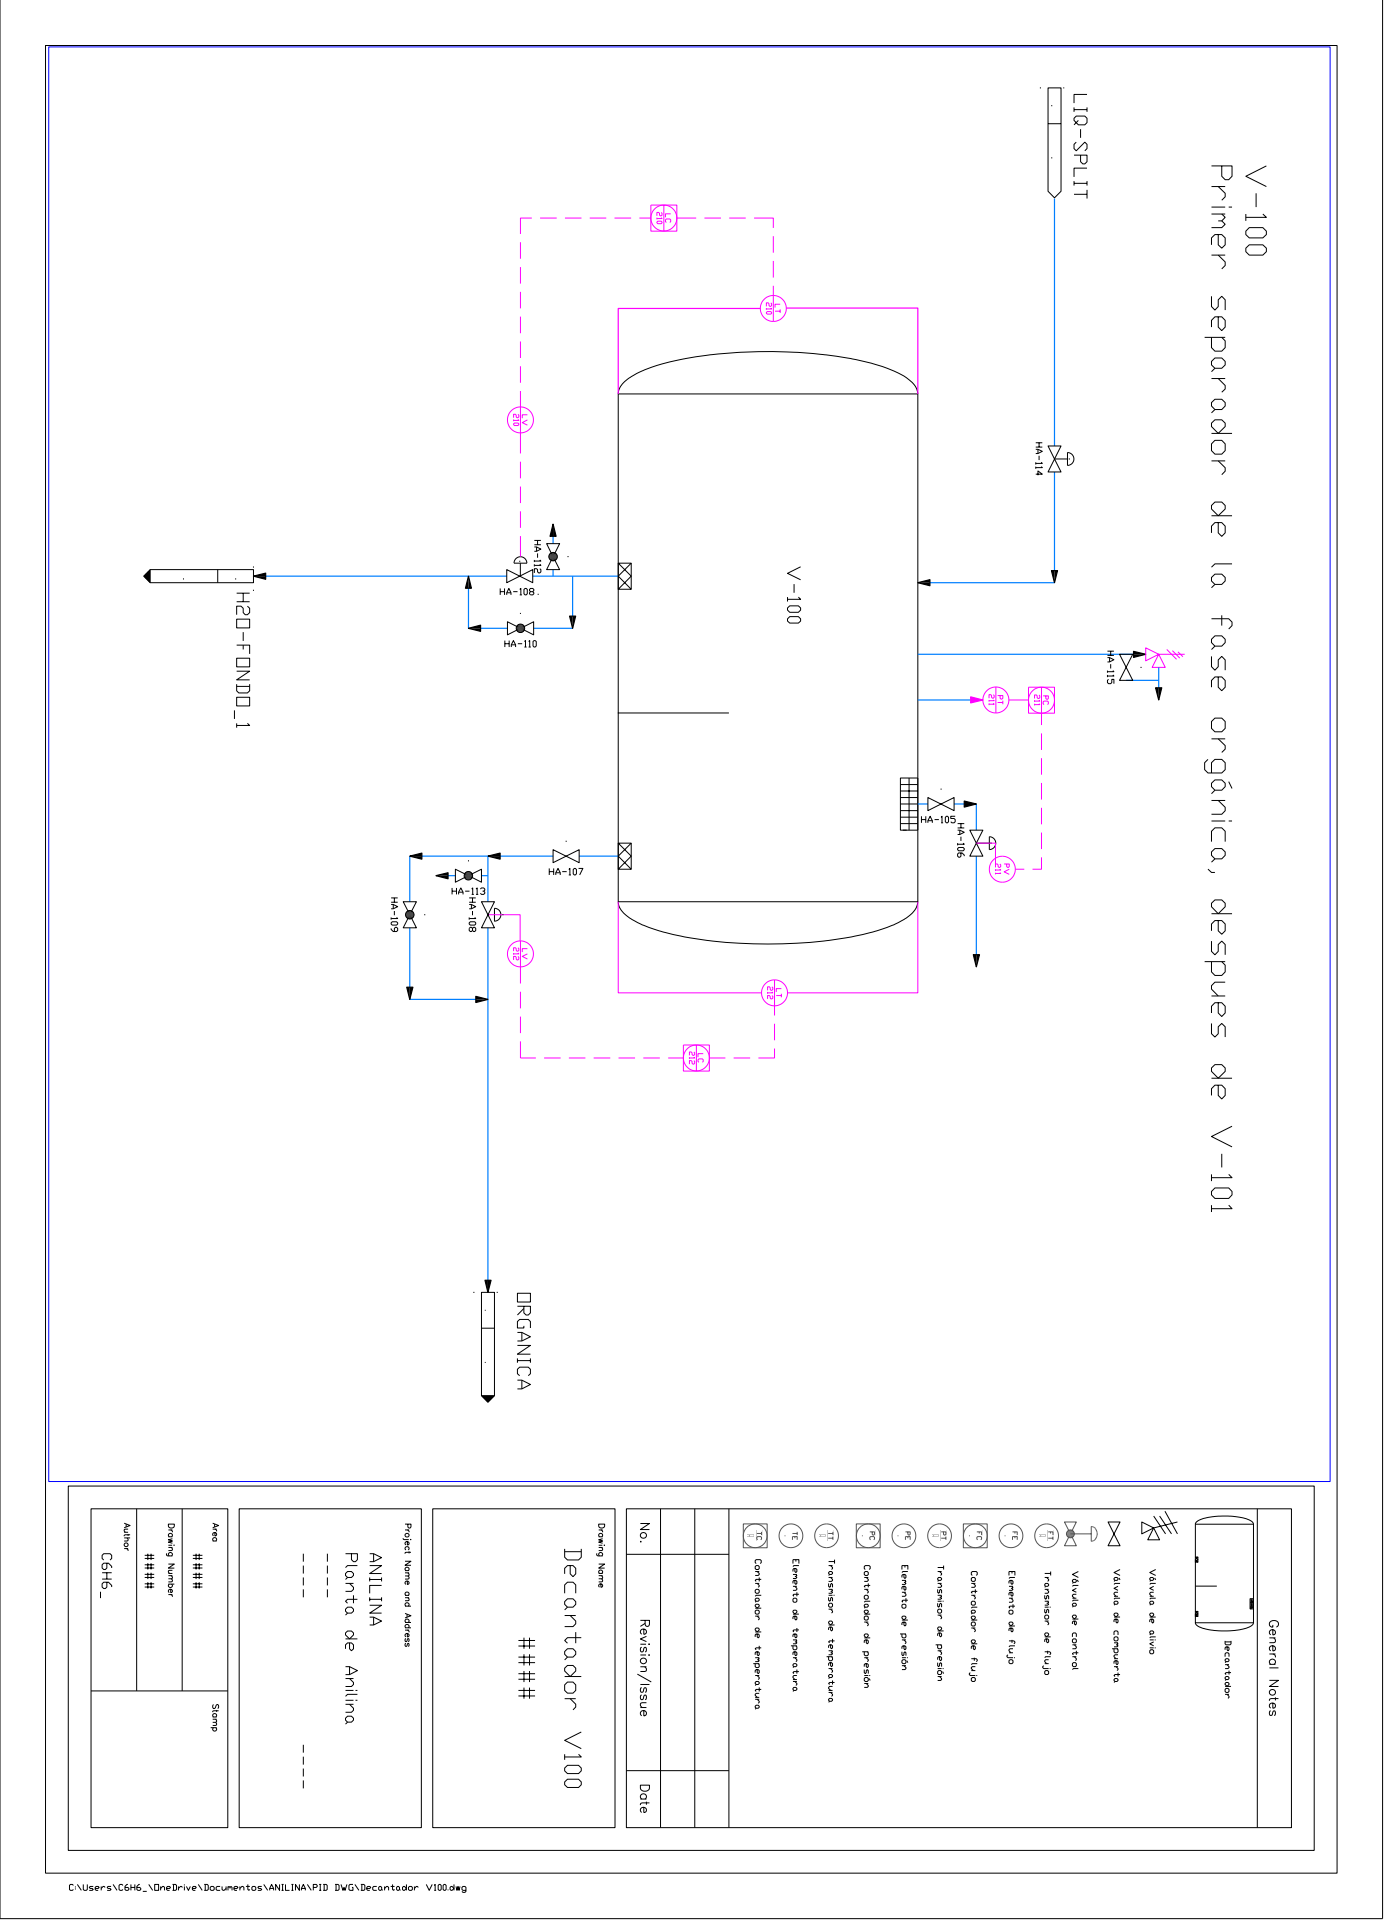
[picture p24: page 1]
